IowaScaledEngineering/ard-ltc2499/pg/ard-ltc2499-v1.1-r802/ard-ltc2499-pcb.pdf

# ard-ltc2499.pcb

# 1. Table of Contents (This Page) Created on Tue Apr 22 20:57:30 2014

# 2. component 3. solder 4. outline 5. plated-drill 6. componentmask 7. soldermask 8. topsilk 9. bottomsilk 10. toppaste 11. topassembly 12. bottomassembly 13. fab

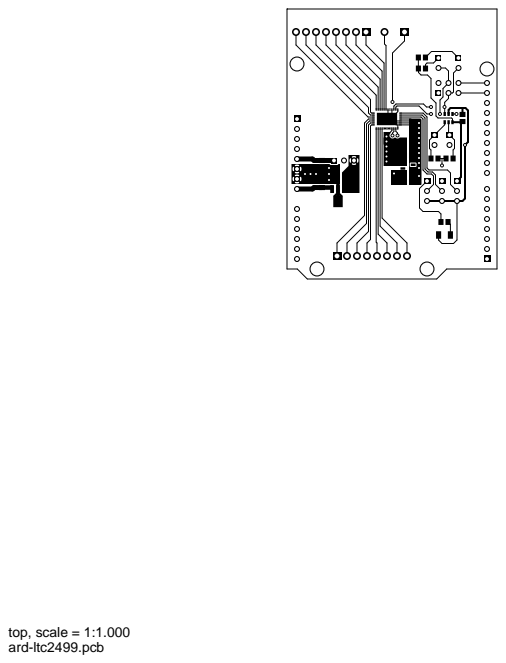
[picture p63: page 2]
top, scale = 1:1.000

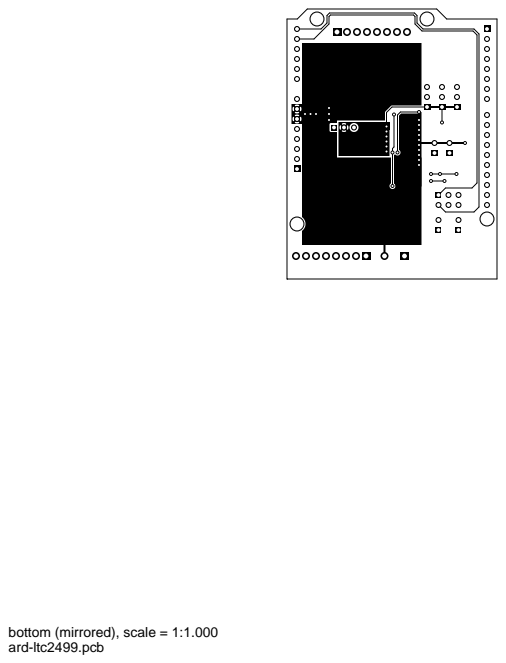
[picture p64: page 3]

bottom (mirrored), scale = 1:1.000

outline, scale = 1:1.000


plated-drill, scale = 1:1.000

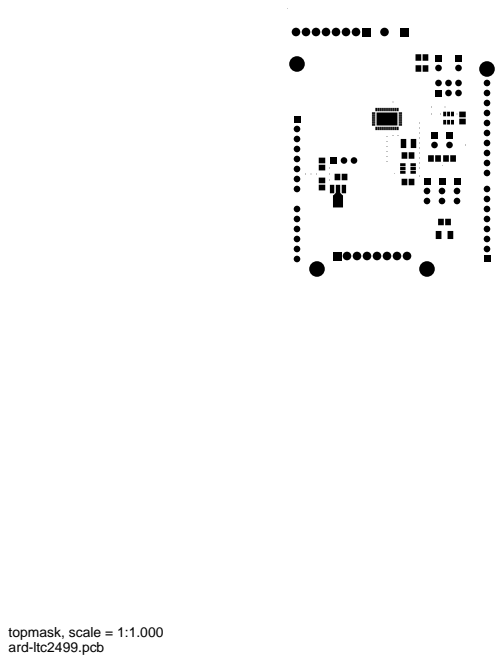
[picture p65: page 6]
topmask, scale = 1:1.000


bottommask (mirrored), scale = 1:1.000

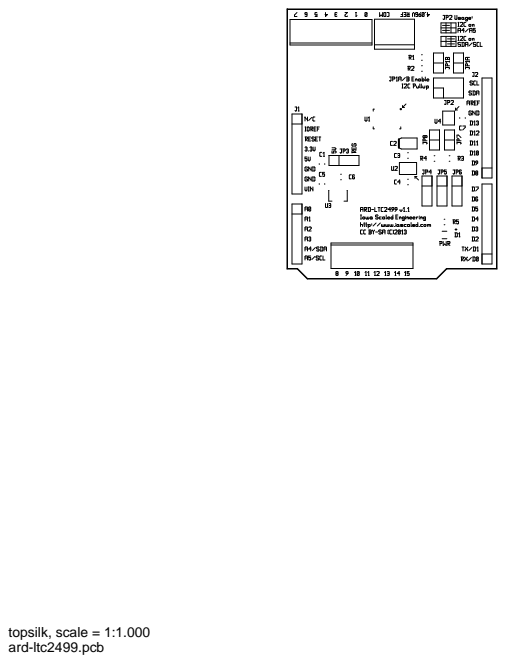
[picture p66: page 8]
topsilk, scale = 1:1.000

bottomsilk (mirrored), scale = 1:1.000

toppaste, scale = 1:1.000

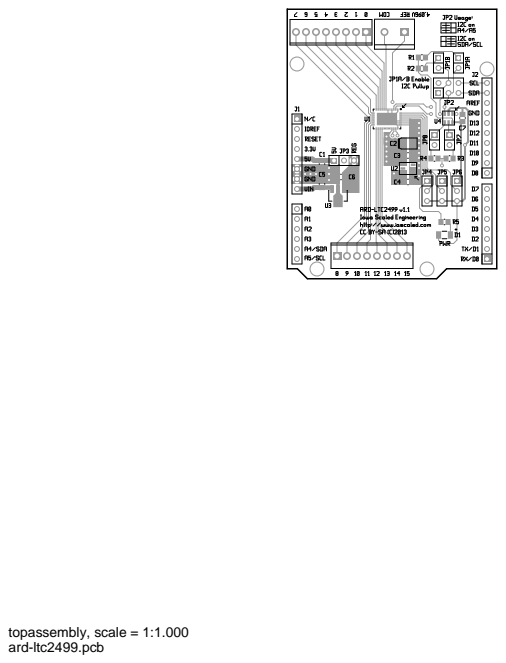
[picture p67: page 11]
topassembly, scale = 1:1.000

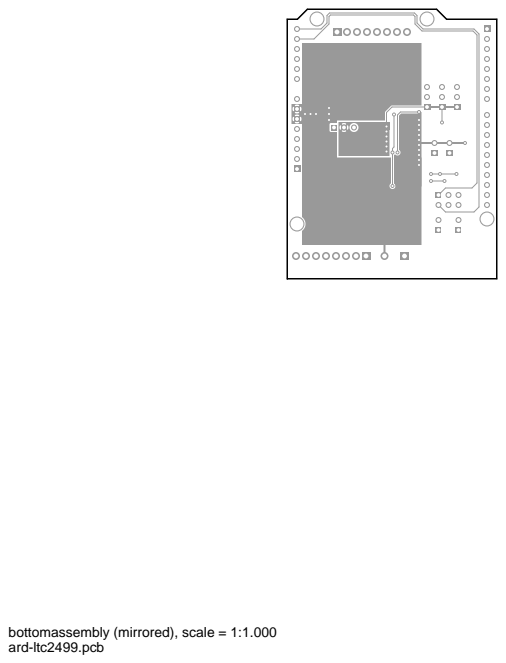
[picture p68: page 12]

bottomassembly (mirrored), scale = 1:1.000

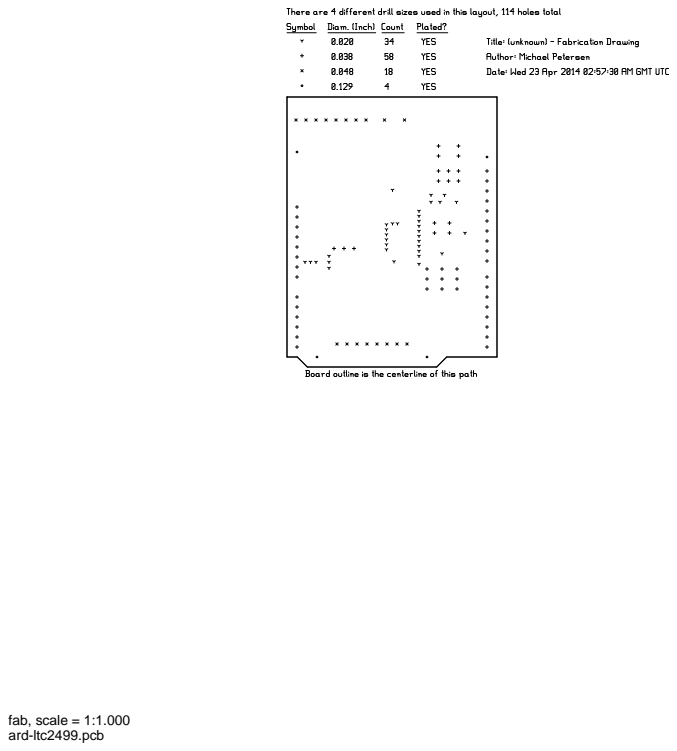
[picture p69: page 13]
fab, scale = 1:1.000
