IowaScaledEngineering/ard-ltc2499/src/Ard2499/examples/ard2499_test/ard2499_test.ino

/*************************************************************************
Title:    ARD-LTC2499 Library Board Test
Authors:  Michael Petersen <railfan@drgw.net>
File:     $Id: $
License:  GNU General Public License v3

LICENSE:
    Copyright (C) 2014 Nathan D. Holmes & Michael D. Petersen

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
*************************************************************************/

/*
  This sketch will demonstrate how to use the Ard2499 library for the 
  Iowa Scaled Engineering ARD-LTC2499 shield.   For more information about the
  ARD-LTC2499, see here:  http://www.iascaled.com/store/ARD-LTC2499
  
  The jumpers for ADC address and EEPROM address should be left open, or the 
  defines for the ADC and EEPROM addresses should be changed in the setup() function.
*/

#include <Wire.h>
#include <Ard2499.h>

#define VREF 4.096

Ard2499 ard2499board1;

byte confChan=0;

void setup() {
  // initialize serial communications at 9600 bps:
  Serial.begin(115200);
  while(!Serial);
  Wire.begin();
  ard2499board1.begin(ARD2499_ADC_ADDR_ZZZ, ARD2499_EEP_ADDR_ZZ, VREF * 1000.0);
  ard2499board1.ltc2499ChangeConfiguration(LTC2499_CONFIG2_60_50HZ_REJ);
  ard2499board1.ltc2499ChangeChannel(LTC2499_CHAN_SINGLE_0P);

}
byte i=0;

void loop() {
  byte retval = 0;

enumerateI2C(true);
//  goto skipJumpers;

/*
  Serial.print("Looking for 0x52 (JP7)... ");
  findI2CSlave(0x52);

  Serial.print("Looking for 0x51 (JP8)... ");
  findI2CSlave(0x51);

  Serial.print("Looking for 0x53 (Open)... ");
  findI2CSlave(0x53);

  Serial.print("Looking for 0x44 (JP4 Bot)... ");
  findI2CSlave(0x44);

  Serial.print("Looking for 0x46 (JP4 Top)... ");
  findI2CSlave(0x46);

  Serial.print("Looking for 0x36 (JP5 Bot)... ");
  findI2CSlave(0x36);

  Serial.print("Looking for 0x54 (JP5 Top)... ");
  findI2CSlave(0x54);

  Serial.print("Looking for 0x24 (JP6 Bot)... ");
  findI2CSlave(0x24);

  Serial.print("Looking for 0x66 (JP6 Top)... ");
  findI2CSlave(0x66);

  Serial.print("Looking for 0x45 (Open)... ");
  findI2CSlave(0x45);
*/

  Serial.print("Looking for 0x50 (xxx)... ");
  findI2CSlave(0x50);

  Serial.print("Looking for 0x51 (A0)... ");
  findI2CSlave(0x51);

  Serial.print("Looking for 0x53 (A1)... ");
  findI2CSlave(0x53);

  Serial.print("Looking for 0x16 (CA0 L)... ");
  findI2CSlave(0x16);

  Serial.print("Looking for 0x15 (CA0 H)... ");
  findI2CSlave(0x15);

  Serial.print("Looking for 0x27 (CA1 L)... ");
  findI2CSlave(0x27);

  Serial.print("Looking for 0x24 (CA1 H)... ");
  findI2CSlave(0x24);

  Serial.print("Looking for 0x66 (CA2 L)... ");
  findI2CSlave(0x66);

  Serial.print("Looking for 0x45 (CA2 H)... ");
  findI2CSlave(0x45);

  ard2499board1.begin(ARD2499_ADC_ADDR_ZZZ, ARD2499_EEP_ADDR_ZZ, VREF * 1000.0);
  ard2499board1.ltc2499ChangeConfiguration(LTC2499_CONFIG2_60_50HZ_REJ);
  ard2499board1.ltc2499ChangeChannel(LTC2499_CHAN_SINGLE_0P);

  Serial.print("eeprom mac = [");
  Serial.print(ard2499board1.eui48Get());
  Serial.print("]\n");
  
  Serial.print("write eeprom[0] 0x");
  Serial.print(0xAA, HEX);
  retval = ard2499board1.eepromWrite(0, 0xAA, true);
  Serial.print(" retval=");
  Serial.print(retval);
  Serial.print("\n");

  Serial.print("read eeprom[0] 0x");
  Serial.print(ard2499board1.eepromRead(0, true), HEX);
  Serial.print("\n");

  Serial.print("write eeprom[0] 0x");
  Serial.print(0x55, HEX);
  retval = ard2499board1.eepromWrite(0, 0x55, true);
  Serial.print(" retval=");
  Serial.print(retval);
  Serial.print("\n");

  Serial.print("read eeprom[0] 0x");
  Serial.print(ard2499board1.eepromRead(0, true), HEX);
  Serial.print("\n");

  delay(1000);

skipJumpers:

  for(i=0; i<17; i++)
  {
    byte newChannel;
    byte adjacentChannel;
    switch(i)
    {
       case 0:
          newChannel = LTC2499_CHAN_SINGLE_0P;
          adjacentChannel = LTC2499_CHAN_SINGLE_1P;
          break;
          
       case 1:
          newChannel = LTC2499_CHAN_SINGLE_1P;
          adjacentChannel = LTC2499_CHAN_SINGLE_2P;
          break;

       case 2:
          newChannel = LTC2499_CHAN_SINGLE_2P;
          adjacentChannel = LTC2499_CHAN_SINGLE_3P;
          break;

       case 3:
          newChannel = LTC2499_CHAN_SINGLE_3P;
          adjacentChannel = LTC2499_CHAN_SINGLE_4P;
          break;

       case 4:
          newChannel = LTC2499_CHAN_SINGLE_4P;
          adjacentChannel = LTC2499_CHAN_SINGLE_5P;
          break;
          
       case 5:
          newChannel = LTC2499_CHAN_SINGLE_5P;
          adjacentChannel = LTC2499_CHAN_SINGLE_6P;
          break;

       case 6:
          newChannel = LTC2499_CHAN_SINGLE_6P;
          adjacentChannel = LTC2499_CHAN_SINGLE_7P;
          break;

       case 7:
          newChannel = LTC2499_CHAN_SINGLE_7P;
          adjacentChannel = LTC2499_CHAN_SINGLE_8P;
          break;

       case 8:
          newChannel = LTC2499_CHAN_SINGLE_8P;
          adjacentChannel = LTC2499_CHAN_SINGLE_9P;
          break;
          
       case 9:
          newChannel = LTC2499_CHAN_SINGLE_9P;
          adjacentChannel = LTC2499_CHAN_SINGLE_10P;
          break;

       case 10:
          newChannel = LTC2499_CHAN_SINGLE_10P;
          adjacentChannel = LTC2499_CHAN_SINGLE_11P;
          break;

       case 11:
          newChannel = LTC2499_CHAN_SINGLE_11P;
          adjacentChannel = LTC2499_CHAN_SINGLE_12P;
          break;

       case 12:
          newChannel = LTC2499_CHAN_SINGLE_12P;
          adjacentChannel = LTC2499_CHAN_SINGLE_13P;
          break;

       case 13:
          newChannel = LTC2499_CHAN_SINGLE_13P;
          adjacentChannel = LTC2499_CHAN_SINGLE_14P;
          break;

       case 14:
          newChannel = LTC2499_CHAN_SINGLE_14P;
          adjacentChannel = LTC2499_CHAN_SINGLE_15P;
          break;

       case 15:
          newChannel = LTC2499_CHAN_SINGLE_15P;
          adjacentChannel = LTC2499_CHAN_SINGLE_0P;  // Bogus
          break;

       case 16:
       default:
          newChannel = LTC2499_CHAN_TEMPERATURE;
          break;

    }

    long adc = 0;
    ard2499board1.ltc2499ChangeChannel(newChannel);

    if (i > 15)
    {
      Serial.print("LTC2499 Temperature");
      Serial.print(" = [");
      Serial.print(ard2499board1.ltc2499ReadTemperature(ARD2499_TEMP_F));
      Serial.print(" F]\n");

      ard2499board1.ltc2499ChangeChannel(LTC2499_CHAN_SINGLE_0P);
      adc = ard2499board1.ltc2499Read();
      Serial.print("Channel 0 Voltage = ");
      Serial.print(" = [");
      Serial.print((VREF/2.0) * (adc / 16777216.0), 3);
      Serial.print(" V] (Expect ~ 1.625V)");

      float voltage = ard2499board1.ltc2499ReadVoltage();
      Serial.print(" [");
      Serial.print(ard2499board1.ltc2499ReadVoltage(), 3);
      Serial.print(" V]\n");

      i = 15;  // Stay on temperature
      delay(1000);
    }
    else
    {
      uint8_t count = 0;
      Serial.print("Channel ");
      Serial.print(i);
      do
      {
        adc = ard2499board1.ltc2499Read();
//        Serial.println(adc);
        if((-500 < adc) && (adc < 500))
        {
          count++;
          Serial.print("\a");
          Serial.print("+");
        }
        else
        {
          count = 0;
          Serial.print(".");
        }
      } while(count < 3);

      // Check that it's not shorted to the adjacent channel
      ard2499board1.ltc2499ChangeChannel(adjacentChannel);

      count = 0;
      do
      {
        adc = ard2499board1.ltc2499Read();
//        Serial.println(adc);
        if((adc < -500) || (500 < adc))
        {
          count++;
          Serial.print("|");
        }
        else
        {
          count = 0;
          Serial.print("-");
        }
      } while(count < 3);

      // Verify it's still shorted to original channel
      ard2499board1.ltc2499ChangeChannel(newChannel);

      count = 0;
      do
      {
        adc = ard2499board1.ltc2499Read();
//        Serial.println(adc);
        if((-500 < adc) && (adc < 500))
        {
          count++;
          Serial.print("+");
        }
        else
        {
          count = 0;
          Serial.print(".");
        }
      } while(count < 1);
      
      Serial.print("\a");
      Serial.println(" Done!");
    }
  }
}

void findI2CSlave(uint8_t addr)
{
  byte stat, done = 0;
  while(!done)
  {
    Wire.beginTransmission(addr);
    stat = Wire.endTransmission();
    if(!stat)
    {
      Serial.print("\a");
      Serial.println("Done!");
      done = 1;
    }
  }
  delay(500);
}

byte enumerateI2C(boolean showErrors)
{
  byte addr, stat, last_ack = 0x00;
 
  Serial.print("Enumerating all I2C devices\n (Press any key to stop scanning I2C bus)\n-------------\n");
 
  for(addr=0x00; addr<0x7F; addr++)
  {
    Wire.beginTransmission(addr);
    stat = Wire.endTransmission();
    if(stat)
    {
      if(showErrors)
      {
        Serial.print("0x");
        Serial.print(addr, HEX);
        Serial.print(": ");
        Serial.print(stat);
        Serial.print("\n");
      }
    }  
    else
    {   
      Serial.print("0x");
      Serial.print(addr, HEX);
      Serial.print(" ");
      last_ack = addr;   
    }
  }  
  Serial.print("\n");
  return last_ack;
}
 
